rorosaurus/FurretTotem/src/FurretTotem/GifAnim_Impl.h

// when including in other code, allow disabling all those inits
// to avoid double inits.
#ifndef GIFANIM_INCLUDE
#include "animatedgif_config.h"
#endif

// Use NeoMatrix backend? Defined in main ino that calls sav_loop
#ifdef NEOMATRIX
// select which NEOMATRIX config will be selected
    //#define M16BY16T4
    #include "neomatrix_config.h"
// else use SmartMatrix as defined in config.h
#else
    SMARTMATRIX_ALLOCATE_BUFFERS(matrix, kMatrixWidth, kMatrixHeight, kRefreshDepth, kDmaBufferRows, kPanelType, kMatrixOptions);
    SMARTMATRIX_ALLOCATE_BACKGROUND_LAYER(backgroundLayer, kMatrixWidth, kMatrixHeight, COLOR_DEPTH, kBackgroundLayerOptions);
    #ifdef ENABLE_SCROLLING
    SMARTMATRIX_ALLOCATE_SCROLLING_LAYER(scrollingLayer, kMatrixWidth, kMatrixHeight, COLOR_DEPTH, kScrollingLayerOptions);
    #endif
#endif // NEOMATRIX


#include "GifDecoder.h"

// Used by SimpleGifAnimViewer2 to work without FilenameFunctions*
#ifdef BASICSPIFFS
File file;
bool fileSeekCallback(unsigned long position) { return file.seek(position); }
unsigned long filePositionCallback(void) { return file.position(); }
int fileReadCallback(void) { return file.read(); }
int fileReadBlockCallback(void * buffer, int numberOfBytes) { return file.read((uint8_t*)buffer, numberOfBytes); }
#else
extern File file;
#include "FilenameFunctions.h"
#endif

void die(const char *mesg) {
    Serial.println(mesg);
    delay(100000); // while 1 loop only triggers watchdog on ESP chips
}

/* template parameters are maxGifWidth, maxGifHeight, lzwMaxBits
 * defined in config.h
 */
GifDecoder<128, 64, lzwMaxBits> decoder;

void screenClearCallback(void) {
#ifdef NEOMATRIX
  matrix->clear();
#else
  backgroundLayer.fillScreen({0,0,0});
#endif
}

void updateScreenCallback(void) {
#ifdef NEOMATRIX
  matrix->show();
#else
  backgroundLayer.swapBuffers();
#endif
}

void drawPixelCallback(int16_t x, int16_t y, uint8_t red, uint8_t green, uint8_t blue) {
  red   = matrix->gamma[red];
  green = matrix->gamma[green];
  blue  = matrix->gamma[blue];
#if DEBUGLINE
  if (y == DEBUGLINE) {
      Serial.print(x);
      Serial.print(",");
      Serial.print(y);
      Serial.print(">");
      Serial.print(red);
      Serial.print(",");
      Serial.print(green);
      Serial.print(",");
      Serial.print(blue);
      Serial.println("");
  }
  if (y > DEBUGLINE) return;
#endif
#ifdef NEOMATRIX
  CRGB color = CRGB(red, green, blue);
  if (FACTX == 15 && FACTY == 15) {
      matrix->drawPixel(x*1.5+0.5+OFFSETX, y*1.5+0.5+OFFSETY, color);
      if (x % 2 == 0) matrix->drawPixel(x*1.5+1.5+OFFSETX, y*1.5+0.5+OFFSETY, color);
      if (y % 2 == 0) matrix->drawPixel(x*1.5+0.5+OFFSETX, y*1.5+1.5+OFFSETY, color);
      if (x % 2 == 0 && y % 2 == 0) matrix->drawPixel(x*1.5+1.5+OFFSETX, y*1.5+1.5+OFFSETY, color);
  } else if (FACTY == 15) {
      matrix->drawPixel(x+OFFSETX, y*1.5+0.5+OFFSETY, color);
      if (y % 2 == 0) matrix->drawPixel(x+OFFSETX, y*1.5+1.5+OFFSETY, color);
  } else if (FACTX == 15) {
      matrix->drawPixel(x*1.5+0.5+OFFSETX, y+OFFSETY, color);
      if (x % 2 == 0) matrix->drawPixel(x*1.5+1.5+OFFSETX, y+OFFSETY, color);
  } else {
      matrix->drawPixel(x+OFFSETX, y+OFFSETY, color);
  }
#else
  backgroundLayer.drawPixel(x, y, {red, green, blue});
#endif
}

// Setup method runs once, when the sketch starts
void sav_setup() {
    decoder.setScreenClearCallback(screenClearCallback);
    decoder.setUpdateScreenCallback(updateScreenCallback);
    decoder.setDrawPixelCallback(drawPixelCallback);

    decoder.setFileSeekCallback(fileSeekCallback);
    decoder.setFilePositionCallback(filePositionCallback);
    decoder.setFileReadCallback(fileReadCallback);
    decoder.setFileReadBlockCallback(fileReadBlockCallback);

// when including in other code, allow disabling all those inits
// to avoid double inits.
#ifndef GIFANIM_INCLUDE
    #ifdef NEOMATRIX
	matrix_setup();
    #else
	// neomatrix_config takes care of starting Serial, but we don't call it in the SMARTMATRIX code path
	Serial.begin(115200);
	Serial.println("Running on Native SmartMatrix Backend");
	// Initialize matrix
	matrix.addLayer(&backgroundLayer); 
	matrix.setBrightness(defaultBrightness);

	// for large panels, may want to set the refresh rate lower to leave more CPU time to decoding GIFs (needed if GIFs are playing back slowly)
	//matrix.setRefreshRate(90);
	#if defined(ESP32)
	    // for large panels on ESP32, may want to set the max percentage time dedicated to updating the refresh frames lower, to leave more CPU time to decoding GIFs (needed if GIFs are playing back slowly)
	    matrix.setMaxCalculationCpuPercentage(90);

	    // alternatively, for large panels on ESP32, may want to set the calculation refresh rate divider lower to leave more CPU time to decoding GIFs (needed if GIFs are playing back slowly) - this has the same effect as matrix.setMaxCalculationCpuPercentage() but is set with a different parameter
	    //matrix.setCalcRefreshRateDivider(4);
	    #if defined(SPI_FFS)
		matrix.begin();
	    #else
		// The ESP32 SD Card library is going to want to malloc about 28000 bytes of DMA-capable RAM
		// make sure at least that much is left free
		matrix.begin(28000);
	    #endif
	#else // ESP32
	    matrix.begin();
	#endif // ESP32
    #endif // NEOMATRIX
#endif // GIFANIM_INCLUDE

#ifndef FSOSD
    // SPIFFS Begin (can crash/conflict with IRRemote on ESP32)
    #ifdef FSOFAT
        // Limit Fat support to a single concurrent file to save RAM
	// 37248 KB are saved by using limiting to 1 file instead of 10
        #ifdef GIFANIM_INCLUDE
	    if (!FFat.begin(0, "", 1)) die("Fat FS mount failed. Not enough RAM?");
        #else
	    // Need 2 file descriptors instead of 1 for file browser
	    if (!FFat.begin(0, "", 2)) die("Fat FS mount failed. Not enough RAM?");
        #endif
	Serial.println("FatFS Directory listing:");
    #else
        if (!FSO.begin()) die("FS mount failed");
	Serial.println("Directory listing:");
    #endif

    // ESP8266 SPIFFS uses special directory objects
    #ifdef ESP8266
	Dir dir = SPIFFS.openDir("/");
	while (dir.next()) {
	    String fileName = dir.fileName();
	    size_t fileSize = dir.fileSize();
	    Serial.printf("FS File: %s, size: %s\n", fileName.c_str(), String(fileSize).c_str());
	}
    #else
        #if defined(FSOFAT)
            Serial.printf("Total space: %10u\n", FFat.totalBytes());
            Serial.printf("Free space:  %10u\n", FFat.freeBytes());
            File dir = FFat.open(GIF_DIRECTORY);
            if (!dir) die("Can't open  " GIF_DIRECTORY);
            if (!dir.isDirectory()) die( GIF_DIRECTORY ": not a directory");
        #else
	    File dir = FSO.open("/");
        #endif
	while (File file = dir.openNextFile()) {
	    Serial.print("FS File: ");
	    Serial.print(file.name());
	    Serial.print(" Size: ");
	    Serial.println(file.size());
	}
    #endif // ESP8266
    Serial.println();
#else
    if(initSdCard(SD_CS) < 0) {
	#if ENABLE_SCROLLING == 1
	    scrollingLayer.start("No SD card", -1);
	#endif
	die("No SD card");
    }
#endif
}

bool sav_newgif(const char *pathname) {
    if (file) file.close();
    Serial.print(pathname);
    #ifdef ESP8266
    file = SPIFFS.open(pathname, "r");
    #else
    file = FSO.open(pathname);
    #endif
    if (!file) {
        Serial.println(": Error opening GIF file");
	return 1;
    }
    Serial.println(": Opened GIF file, start decoding");
    decoder.startDecoding();
    return 0;
}

bool sav_loop() {
    // ERROR_WAITING means it wasn't time to display the next frame and the display did
    // not get updated (this is important for a neopixel matrix where the display being
    // updated causes a pause in the code).
    if (decoder.decodeFrame() == ERROR_WAITING) return 1;
    return 0;
}

// vim:sts=4:sw=4
